fredriknk/OhmPI/MUX_board/MUX_v2024_relay_board/MUX_1_relay.kicad_sch

## KiCad design MUX_board/MUX_v2024_relay_board/MUX_1_relay.kicad_sch (2022-11-21)

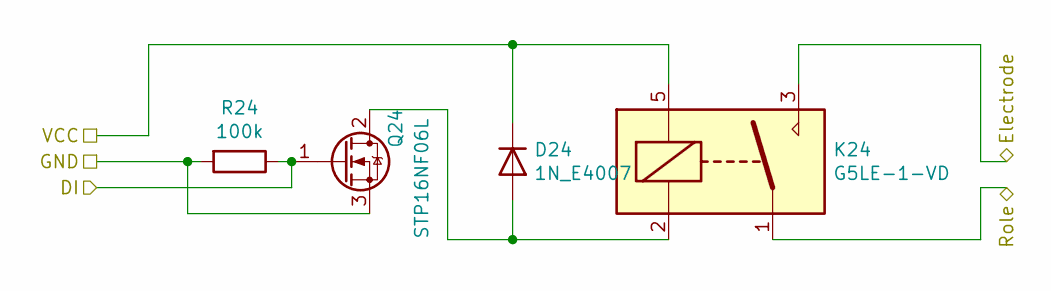
[picture p17: schematic MUX_1_relay.kicad_sch]

Parts:
D24: 1N_E4007; D_DO-41_SOD81_P10.16mm_Horizontal
K24: G5LE-1-VD; Relay_SPDT_Omron-G5LE-1-VD
Q24: STP16NF06L; TO-220-3_Vertical
R24: 100k; R_Axial_DIN0207_L6.3mm_D2.5mm_P15.24mm_Horizontal

Connections:
DI: Q24.1 (G), R24.1
Electrode: K24.3
GND: Q24.3 (S), R24.2
unnamed: D24.2 (A), K24.2, Q24.2 (D)
Role: K24.1
VCC: D24.1 (K), K24.5
